raleighslack/RaraTC/main/communication.c

#include "communication.h"

char *TAG = "BLE-Server";
uint8_t ble_addr_type;
void ble_app_advertise(void);// Write data to ESP32 defined as server

static int device_write(uint16_t conn_handle, uint16_t attr_handle, struct ble_gatt_access_ctxt *ctxt, void *arg)
{
    // printf("Data from the client: %.*s\n", ctxt->om->om_len, ctxt->om->om_data);

    char * data = (char *)ctxt->om->om_data;
    printf("%d\n",strcmp(data, (char *)"LIGHT ON")==0);
    if (strcmp(data, (char *)"LIGHT ON\0")==0)
    {
       printf("LIGHT ON\n");
    }
    else if (strcmp(data, (char *)"LIGHT OFF\0")==0)
    {
        printf("LIGHT OFF\n");
    }
    else if (strcmp(data, (char *)"FAN ON\0")==0)
    {
        printf("FAN ON\n");
    }
    else if (strcmp(data, (char *)"FAN OFF\0")==0)
    {
        printf("FAN OFF\n");
    }
    else{
        printf("Data from the client: %.*s\n", ctxt->om->om_len, ctxt->om->om_data);
    }
    
    
    return 0;
}

// Read data from ESP32 defined as server
static int device_read(uint16_t con_handle, uint16_t attr_handle, struct ble_gatt_access_ctxt *ctxt, void *arg)
{
    os_mbuf_append(ctxt->om, "1", strlen("1"));
    return 0;
}

static int lipo_ble_read(uint16_t con_handle, uint16_t attr_handle, struct ble_gatt_access_ctxt *ctxt, void *arg)
{
    // float voltage = get_lipo_voltage();
    // char float_bytes[sizeof(voltage)];
    // memcpy(float_bytes, &voltage, sizeof(voltage));
    // os_mbuf_append(ctxt->om, float_bytes, sizeof(voltage));
    // return 0;
    int percent = get_lipo_percent();
    os_mbuf_append(ctxt->om, &percent, sizeof(percent));
    return 0;
}

// BLE event handling
static int ble_gap_event(struct ble_gap_event *event, void *arg)
{
    switch (event->type)
    {
    // Advertise if connected
    case BLE_GAP_EVENT_CONNECT:
        ESP_LOGI("GAP", "BLE GAP EVENT CONNECT %s", event->connect.status == 0 ? "OK!" : "FAILED!");
        if (event->connect.status != 0)
        {
            ble_app_advertise();
        }
        break;
    // Advertise again after completion of the event
    case BLE_GAP_EVENT_DISCONNECT:
        ESP_LOGI("GAP", "BLE GAP EVENT DISCONNECTED");
        // ble_app_advertise();
        break;
    case BLE_GAP_EVENT_ADV_COMPLETE:
        ESP_LOGI("GAP", "BLE GAP EVENT");
        ble_app_advertise();
        break;
    default:
        break;
    }
    return 0;
}

// Define the BLE connection
void ble_app_advertise(void)
{
    // GAP - device name definition
    struct ble_hs_adv_fields fields;
    const char *device_name;
    memset(&fields, 0, sizeof(fields));
    device_name = ble_svc_gap_device_name(); // Read the BLE device name
    fields.name = (uint8_t *)device_name;
    fields.name_len = strlen(device_name);
    fields.name_is_complete = 1;
    ble_gap_adv_set_fields(&fields);

    // GAP - device connectivity definition
    struct ble_gap_adv_params adv_params;
    memset(&adv_params, 0, sizeof(adv_params));
    adv_params.conn_mode = BLE_GAP_CONN_MODE_UND; // connectable or non-connectable
    adv_params.disc_mode = BLE_GAP_DISC_MODE_GEN; // discoverable or non-discoverable
    ble_gap_adv_start(ble_addr_type, NULL, BLE_HS_FOREVER, &adv_params, ble_gap_event, NULL);
}

// The application
void ble_app_on_sync(void)
{
    ble_hs_id_infer_auto(0, &ble_addr_type); // Determines the best address type automatically
    ble_app_advertise();                     // Define the BLE connection
}

// The infinite task
void host_task(void *param)
{
    nimble_port_run(); // This function will return only when nimble_port_stop() is executed
}

esp_err_t bluetooth_main(const char* name)
{
    esp_err_t errorState = ESP_OK;
    // errorState += nvs_flash_init();         // 1 - Initialize NVS flash using
    // esp_nimble_hci_and_controller_init();   // 2 - Initialize ESP controller
    errorState = nimble_port_init();           // 3 - Initialize the host stack
    ble_svc_gap_device_name_set(name);         // 4 - Initialize NimBLE configuration - server name
    ble_svc_gap_init();                        // 4 - Initialize NimBLE configuration - gap service
    ble_svc_gatt_init();                       // 4 - Initialize NimBLE configuration - gatt service
    ble_gatts_count_cfg(gatt_svcs);            // 4 - Initialize NimBLE configuration - config gatt services
    ble_gatts_add_svcs(gatt_svcs);             // 4 - Initialize NimBLE configuration - queues gatt services.
    ble_hs_cfg.sync_cb = ble_app_on_sync;      // 5 - Initialize application
    nimble_port_freertos_init(host_task);      // 6 - Run the thread
    return errorState;
}

esp_err_t ble_deinit()
{
    esp_err_t errorState = ESP_OK;
    errorState += nimble_port_deinit();
    errorState += nvs_flash_deinit();
    return errorState;
}
