raleighslack/RaraTC/main/communication.h

#pragma once

#include <stdio.h>
#include "freertos/FreeRTOS.h"
#include "freertos/task.h"
#include "freertos/event_groups.h"
#include "esp_event.h"
#include "nvs_flash.h"
#include "esp_log.h"
#include "esp_nimble_hci.h"
#include "nimble/nimble_port.h"
#include "nimble/nimble_port_freertos.h"
#include "host/ble_hs.h"
#include "services/gap/ble_svc_gap.h"
#include "services/gatt/ble_svc_gatt.h"
#include "sdkconfig.h"
#include "lipo.h"

void ble_app_advertise(void);
static int device_write(uint16_t conn_handle, uint16_t attr_handle, struct ble_gatt_access_ctxt *ctxt, void *arg);
static int device_read(uint16_t con_handle, uint16_t attr_handle, struct ble_gatt_access_ctxt *ctxt, void *arg);
static int lipo_ble_read(uint16_t con_handle, uint16_t attr_handle, struct ble_gatt_access_ctxt *ctxt, void *arg);
static int ble_gap_event(struct ble_gap_event *event, void *arg);
void ble_app_advertise(void);
void ble_app_on_sync(void);
void host_task(void *param);
esp_err_t ble_deinit();

// Array of pointers to other service definitions
// UUID - Universal Unique Identifier
static const struct ble_gatt_svc_def gatt_svcs[] = {
    {.type = BLE_GATT_SVC_TYPE_PRIMARY,
     .uuid = BLE_UUID16_DECLARE(0x180),                 // Define UUID for device type
     .characteristics = (struct ble_gatt_chr_def[]){
         {.uuid = BLE_UUID16_DECLARE(0xFEF4),           // Define UUID for reading
          .flags = BLE_GATT_CHR_F_READ,
          .access_cb = device_read},
          {.uuid = BLE_UUID16_DECLARE(0xBEBE),           // Define UUID for reading
          .flags = BLE_GATT_CHR_F_READ,
          .access_cb = lipo_ble_read},
         {.uuid = BLE_UUID16_DECLARE(0xDEAD),           // Define UUID for writing
          .flags = BLE_GATT_CHR_F_WRITE,
          .access_cb = device_write},
         {0}}},
    {0}};

esp_err_t bluetooth_main();
